mihranrazaa/KBoard/Assets/screenshot_20260409_134038.jpg

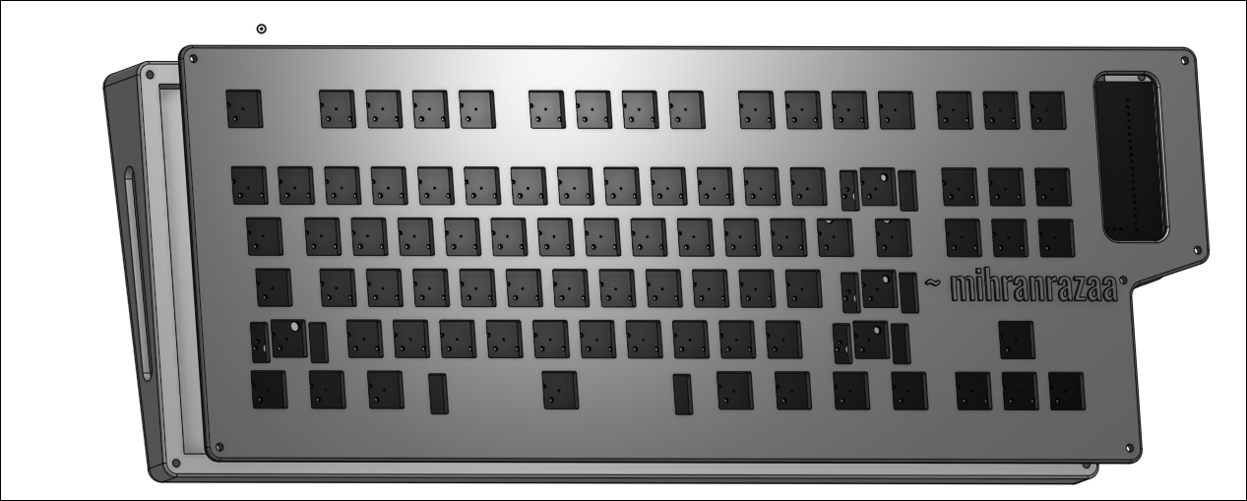
Assets/screenshot_20260409_134038.jpg
